nyarurato/ble_stepper_motor_analyzer/docs/MDBT42Q Footprint_Design Guide-210702/MDBT42Q Footprint/MDBT42Q Altium Library/MDBT42Q Altium Library-210702.jpg

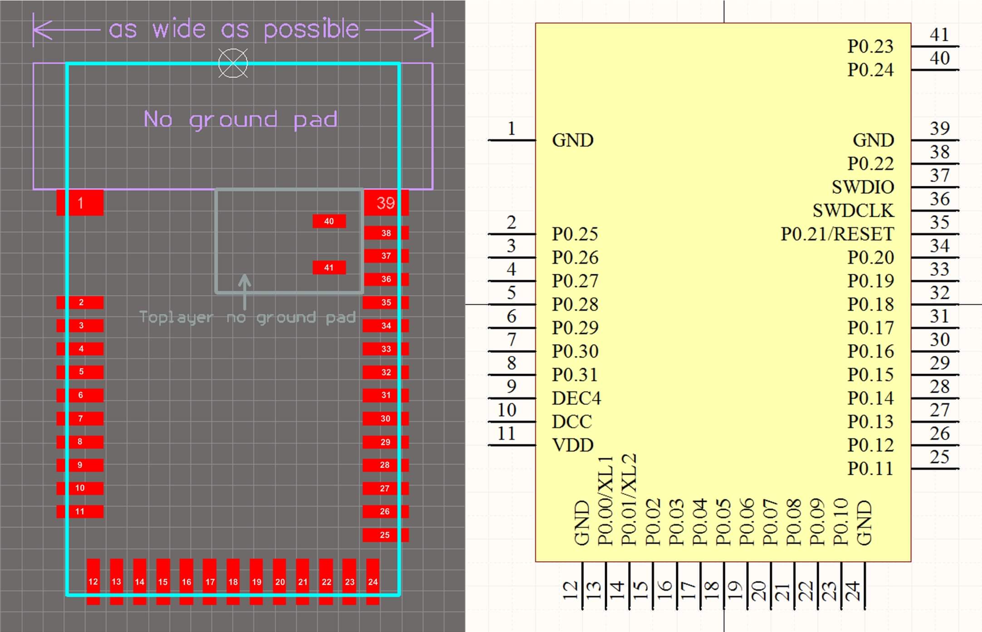
docs/MDBT42Q Footprint_Design Guide-210702/MDBT42Q Footprint/MDBT42Q Altium Library/MDBT42Q Altium Library-210702.jpg
