nyarurato/ble_stepper_motor_analyzer/docs/MDBT42Q Footprint_Design Guide-210702/Reflow (solder profile)-nRF52832 Module (EN).png

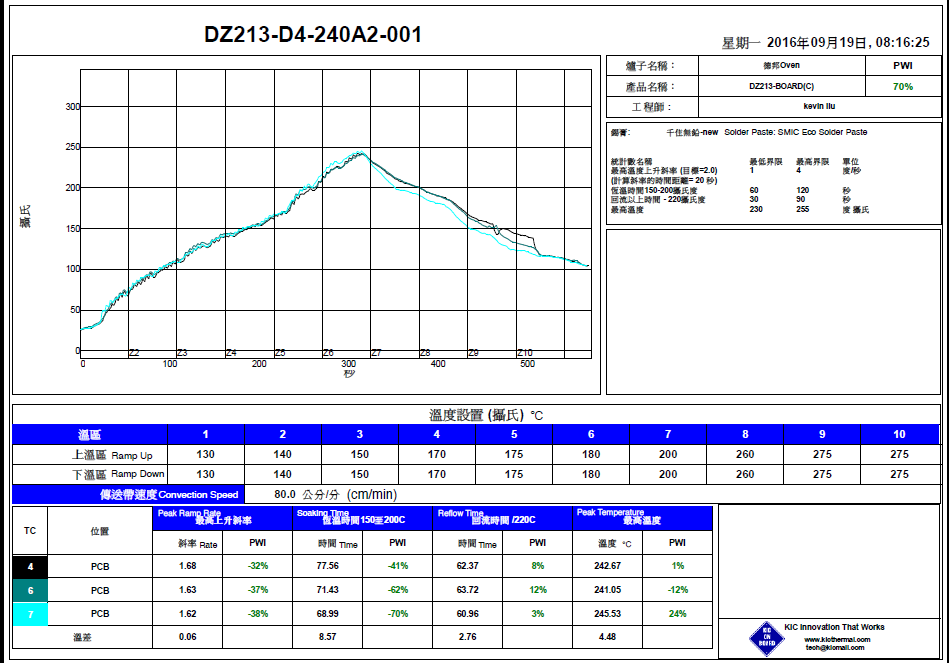
docs/MDBT42Q Footprint_Design Guide-210702/Reflow (solder profile)-nRF52832 Module (EN).png
